eutectic6337/coin1/software/coin-chase3/sequence_fixed_length.c

/*
 * sequence_fixed_length.c
 *
 *  Created on: Jul 17, 2025
 *      Author: mlp
 *
 *  LED sequences which can be represented as a fixed-length array of patterns
 */
#if SEQUENCE_FIXED_LENGTH == 1
#include "sequence.h"
#define SELECTED_SEQUENCE chase

#include "debug.h"
#include "utility.h"

const struct pattern chase[] = {
	{{100,  0,  0,  0,  0,  0,  0,  0,  0,  0,  0,  0,  0,  0,  0,  0}, 100},//[0]
	{{100,100,  0,  0,  0,  0,  0,  0,  0,  0,  0,  0,  0,  0,  0,  0}, 100},
	{{  0,100,  0,  0,  0,  0,  0,  0,  0,  0,  0,  0,  0,  0,  0,  0}, 100},
	{{  0,100,100,  0,  0,  0,  0,  0,  0,  0,  0,  0,  0,  0,  0,  0}, 100},
	{{  0,  0,100,  0,  0,  0,  0,  0,  0,  0,  0,  0,  0,  0,  0,  0}, 100},
	{{  0,  0,100,100,  0,  0,  0,  0,  0,  0,  0,  0,  0,  0,  0,  0}, 100},
	{{  0,  0,  0,100,  0,  0,  0,  0,  0,  0,  0,  0,  0,  0,  0,  0}, 100},
	{{  0,  0,  0,100,100,  0,  0,  0,  0,  0,  0,  0,  0,  0,  0,  0}, 100},
	{{  0,  0,  0,  0,100,  0,  0,  0,  0,  0,  0,  0,  0,  0,  0,  0}, 100},
	{{  0,  0,  0,  0,100,100,  0,  0,  0,  0,  0,  0,  0,  0,  0,  0}, 100},
	{{  0,  0,  0,  0,  0,100,  0,  0,  0,  0,  0,  0,  0,  0,  0,  0}, 100},
	{{  0,  0,  0,  0,  0,100,100,  0,  0,  0,  0,  0,  0,  0,  0,  0}, 100},
	{{  0,  0,  0,  0,  0,  0,100,  0,  0,  0,  0,  0,  0,  0,  0,  0}, 100},
	{{  0,  0,  0,  0,  0,  0,100,100,  0,  0,  0,  0,  0,  0,  0,  0}, 100},
	{{  0,  0,  0,  0,  0,  0,  0,100,  0,  0,  0,  0,  0,  0,  0,  0}, 100},
	{{  0,  0,  0,  0,  0,  0,  0,100,100,  0,  0,  0,  0,  0,  0,  0}, 100},
	{{  0,  0,  0,  0,  0,  0,  0,  0,100,  0,  0,  0,  0,  0,  0,  0}, 100},
	{{  0,  0,  0,  0,  0,  0,  0,  0,100,100,  0,  0,  0,  0,  0,  0}, 100},
	{{  0,  0,  0,  0,  0,  0,  0,  0,  0,100,  0,  0,  0,  0,  0,  0}, 100},
	{{  0,  0,  0,  0,  0,  0,  0,  0,  0,100,100,  0,  0,  0,  0,  0}, 100},
	{{  0,  0,  0,  0,  0,  0,  0,  0,  0,  0,100,  0,  0,  0,  0,  0}, 100},
	{{  0,  0,  0,  0,  0,  0,  0,  0,  0,  0,100,100,  0,  0,  0,  0}, 100},
	{{  0,  0,  0,  0,  0,  0,  0,  0,  0,  0,  0,100,  0,  0,  0,  0}, 100},
	{{  0,  0,  0,  0,  0,  0,  0,  0,  0,  0,  0,100,100,  0,  0,  0}, 100},
	{{  0,  0,  0,  0,  0,  0,  0,  0,  0,  0,  0,  0,100,  0,  0,  0}, 100},
	{{  0,  0,  0,  0,  0,  0,  0,  0,  0,  0,  0,  0,100,100,  0,  0}, 100},
	{{  0,  0,  0,  0,  0,  0,  0,  0,  0,  0,  0,  0,  0,100,  0,  0}, 100},
	{{  0,  0,  0,  0,  0,  0,  0,  0,  0,  0,  0,  0,  0,100,100,  0}, 100},
	{{  0,  0,  0,  0,  0,  0,  0,  0,  0,  0,  0,  0,  0,  0,100,  0}, 100},
	{{  0,  0,  0,  0,  0,  0,  0,  0,  0,  0,  0,  0,  0,  0,100,100}, 100},
	{{  0,  0,  0,  0,  0,  0,  0,  0,  0,  0,  0,  0,  0,  0,  0,100}, 100},
	{{100,  0,  0,  0,  0,  0,  0,  0,  0,  0,  0,  0,  0,  0,  0,100}, 100},//[31]
};

struct pattern get_next_pattern(void)
{
	static const struct pattern *sequence_start = SELECTED_SEQUENCE;
	static int sequence_length = NUM_ARRAY_ELEMS(SELECTED_SEQUENCE);

	static int sequence_step = 0;


	printf("step %d of %d\r\n", sequence_step, sequence_length);
	if (sequence_step < sequence_length-1) {
		sequence_step++;
	}
	else {
		sequence_step = 0;
	}

	return sequence_start[sequence_step];
}
#else
static int sequence_fixed_length = 0;
#endif
