eutectic6337/coin1/software/coin-chase2/User/sequence_random.c

/*
 * sequence_random.c
 *
 *  Created on: Jul 17, 2025
 *      Author: mlp
 *
 *  produce an infinite series of random patterns
 */
#if SEQUENCE_RANDOM == 1
#include "sequence.h"

#include <stdlib.h>

#define MIN_TIME 10 //ms
#define MAX_TIME 1000
#define MIN_BRIGHT 0 //percent
#define MAX_BRIGHT 100

struct pattern get_next_pattern(void)
{
	struct pattern p = {0};
	p.time = MIN_TIME + random() % (MAX_TIME - MIN_TIME);
	for (int i = 0; i < NUM_LEDS_IN_PATTERN; i++) {
		p.bright[i] = MIN_BRIGHT + random() %(MAX_BRIGHT - MIN_BRIGHT);
	}
	return p;
}
#else
static int sequence_random = 0;
#endif
