eutectic6337/coin1/software/validate2/main/sleepwake.h

/*
 * sleepwake.h
 *
 *  Created on: Feb 21, 2025
 *      Author: mlp
 */

#ifndef SLEEPWAKE_H_
#define SLEEPWAKE_H_

void init_sleepwake(void);
void loop_sleepwake(void);

#endif /* USER_SLEEPWAKE_H_ */
