eutectic6337/coin1/software/Blink/Blink.ino

/*
  Blink
*/

#define NUM_ARRAY_ELEMS(a) ((sizeof a)/(sizeof a[0]))

struct pin_pair {	int p1, p2;	}
const LED_pair_pins[] = {
		{PC5, PC3/*TIM1_CH3*/},
		{PC2, PC0/*TIM2_CH3*/},
		{PC1, PA1/*TIM1_CH2*/},
		{PD0, PD7/*TIM2_CH4*/},
		{PD5, PD4/*TIM2_CH1*/},
		{PD1/*SWIO*/, PD3/*TIM2_CH2*/},
		{PC7, PD2/*TIM1_CH1*/},
		{PC6, PC4/*TIM1_CH4*/},
};

void setup() {
  delay(1000);

	//https://www.eevblog.com/forum/microcontrollers/ch32v003-info/msg5713903/#msg5713903
	AFIO->PCFR1 = AFIO->PCFR1 & 0xFFFF7FFF; //Sets PA1 & PA2 as I/O by clearing bit 15

	FLASH_Unlock();
	FLASH_EraseOptionBytes();
	FLASH_UserOptionByteConfig(OB_STOP_NoRST, OB_STDBY_NoRST, OB_RST_NoEN, /*OB_PowerON_*/Start_Mode_USER);
	FLASH_Lock();

	//To use PD7 as I/O you have to enable it in WCH Link Utility.
	//in dropdown textbox near "Enable Soft-Ctrl- iWDG."
	//option "Disable mul-func, PD7 used for IO function."
	
	for (int i = 0; i < NUM_ARRAY_ELEMS(LED_pair_pins); i++) {
		pinMode(LED_pair_pins[i].p1, OUTPUT);
		pinMode(LED_pair_pins[i].p2, OUTPUT);

		digitalWrite(LED_pair_pins[i].p1, LOW);
		digitalWrite(LED_pair_pins[i].p2, LOW);
	}
}

// the loop function runs over and over again forever
void loop() {
 	for (int i = 0; i < NUM_ARRAY_ELEMS(LED_pair_pins); i++) {
		digitalWrite(LED_pair_pins[i].p2, HIGH);
    delay(1);
		digitalWrite(LED_pair_pins[i].p1, HIGH);
		delay(99);
		digitalWrite(LED_pair_pins[i].p2, LOW);
    delay(1);
		digitalWrite(LED_pair_pins[i].p1, LOW);
		delay(99);
  }
}
