eutectic6337/coin1/software/coin-chase3/utility.h

/*
 * utility.h
 *
 *  Created on: May 22, 2025
 *      Author: mlp
 */

#ifndef USER_UTILITY_H_
#define USER_UTILITY_H_

#define NUM_ARRAY_ELEMS(a) ((sizeof a)/(sizeof a[0]))

#endif /* USER_UTILITY_H_ */
